GlobalFishingWatch/ssf-tracker-prototype/controller/app/app.py

# Main application

from util import default_logger
from util import load_config
from util import save_config
from util import configure_logger
from config import default_app_state

from statemachine import StateMachine
from statemachine import State
from statemachine import Transition
from statemachine import Event
from button import Button
from timer import Timer
# from gps import MockGPS

from wiring import MockWiring


class App(StateMachine):
    states = [
        State('boot'),
        State('idle', on_enter='on_idle'),
        State('locating', on_enter='on_locating'),
        State('sleep', on_enter='on_sleep'),
    ]
    transitions = [
        Transition(event='reset', source='boot', dest='idle', after='on_reset'),
        Transition(event='idle_timeout', source='idle', dest='sleep', condition='can_deep_sleep'),
        Transition(event='timer_wake', source='sleep', dest='idle'),
        Transition(event='btn_wake', source='sleep', dest='idle'),
        Transition(event='btn1_pressed', after='on_btn1_pressed'),
        Transition(event='btn1_released', after='on_btn1_released'),
        Transition(event='gps_timer', source='idle', dest='locating'),
        Transition(event='gps_ready', source='locating', dest='idle', before='on_gps_ready'),
        Transition(event='gps_timeout', source='locating', dest='idle', before='on_gps_failed'),

        # Catch the gps_timer event in case we were not it the `idle` state and can't transition to `locating` state
        Transition(event='gps_timer', after='retry_event'),
    ]

    @classmethod
    def from_settings(cls, settings, wiring_type=MockWiring, **kwargs):
        app_config = load_config(settings)
        log = configure_logger(app_config)
        wiring = wiring_type(config=app_config)
        log.debug('Creating App...')
        app = cls(wiring=wiring, config=app_config, log=log, **kwargs)
        return app

    def __init__(self, wiring, config=None, log=None, **kwargs):
        self.wiring = wiring
        self.config = config if config else {}
        self.log = log if log else default_logger()
        super(App, self).__init__(states=self.states, transitions=self.transitions, log=self.log, **kwargs)

        self.button1 = Button(name="button1", log=self.log,
                              on_press_event=self.get_event('btn1_pressed'),
                              on_release_event=self.get_event('btn1_released'))

        self.idle_timer = Timer(event=self.get_event('idle_timeout'),
                                duration_ms=self.config.get('IDLE_TIMEOUT_MS', 1000),
                                recurring=True)
        # self.gps = MockGPS(on_ready_event=self.get_event('gps_ready'))
        self.gps_timer = Timer(event=self.get_event('gps_timer'),
                               duration_ms=self.config.get('GPS_FIX_INTERVAL_MS', 10000),
                               recurring=True)
        self.locations = []

    def initialize(self):
        self.log.debug(f'{self.name} initialize...')
        self.wiring.btn_down_event = self.button1.get_event('btn_down')
        self.wiring.btn_up_event = self.button1.get_event('btn_up')
        self.wiring.gps_fix_event = self.get_event('gps_ready')
        self.wiring.initialize()
        wake_reason = self.wiring.wake_reason()
        self.log.debug(f'Wake reason: {wake_reason}')
        if wake_reason == 'RESET':
            self.config['app_state'] = default_app_state
            self.schedule_event('reset')
        self.load_state(self.config['app_state'])

    def settings_file_name(self):
        return self.config['SETTINGS_FILE']

    def is_running(self):
        return True

    def max_sleep_time_ms(self, max_sleep_time_ms):
        next_timer = Timer.get_next_timer()
        return next_timer.time_remaining_ms() if next_timer else max_sleep_time_ms

    def lightsleep(self):
        min_time = self.config.get('MIN_LIGHTSLEEP_TIME_MS', 100)
        max_time = self.config.get('MAX_LIGHTSLEEP_TIME_MS', 1000)
        sleep_time = self.max_sleep_time_ms(max_time)
        if sleep_time > min_time:
            self.wiring.lightsleep(sleep_time)

    def run(self):
        self.log.debug(f'{self.name} run...')
        while self.is_running():
            Timer.check_active_timers()
            Event.trigger_scheduled_events()
            self.gps_update()
            self.lightsleep()

    @staticmethod
    def tick():
        Timer.check_active_timers()
        Event.trigger_scheduled_events()

    def on_reset(self, event):
        self.gps_timer.reset()

    def on_idle(self, event):
        self.idle_timer.reset()

    def can_deep_sleep(self, event):
        # can't sleep if
        #    the button is pressed
        #    we are getting a gps fix
        #    we are transmitting a message
        #    there is not enough time before the next timer goes off (because it takes time to restart)

        min_time = self.config.get('MIN_DEEPSLEEP_TIME_MS', 10 * 1000)
        max_time = self.config.get('MAX_DEEPSLEEP_TIME_MS', 10 * 1000)
        sleep_time = self.max_sleep_time_ms(max_time)

        sleep_blocked = (
            self.button1.state.name == 'pressed'
            or self.state.name in ('locating', 'transmitting')
            or sleep_time < min_time
        )
        return not sleep_blocked

    def on_sleep(self, event):
        self.idle_timer.cancel()

        max_deep_sleep_time = self.config.get('MAX_DEEPSLEEP_TIME_MS', 10*1000)

        sleep_time = self.max_sleep_time_ms(max_deep_sleep_time)
        self.config['app_state'] = self.save_state()
        filename = self.settings_file_name()
        if filename:
            save_config(self.config, self.settings_file_name)
        else:
            self.log.debug('Unable to save settings before sleep because no file name is configured')

        # NB: this will sleep for the specified time and then reset the app
        # NB: Control flow will never return from this call unless you are using MockWiring
        self.wiring.deepsleep(sleep_time)

    def on_btn1_pressed(self, event):
        self.wiring.led1 = 1

    def on_btn1_released(self, event):
        self.wiring.led1 = 0

    def on_locating(self, event):
        # start to fix a new gps location
        # self.gps.schedule_event('locate')
        self.wiring.gps_wake()

    def retry_event(self, event):
        # retry an event after a delay
        t = Timer(duration_ms=self.config['RETRY_INTERVAL_MS'],
                  event=event)
        t.reset()

    def on_gps_ready(self, event):
        # self.locations.append(self.gps.last_location)
        # self.gps.schedule_event('sleep')
        location = event.kwargs
        if location:
            self.locations.append(location)
            self.log.debug(location.get('sentence', 'unknown message in gps_ready event'))
        self.wiring.gps_sleep()

    def on_gps_failed(self, event):
        # self.gps.schedule_event('sleep')
        self.wiring.gps_sleep()

    def gps_update(self):
        message = self.wiring.gps_update()
        if message and 'sentence' in message:
            self.log.info(message['message'])

    def save_state(self):
        state = super(App, self).save_state()
        state['button1'] = self.button1.save_state()
        state['idle_timer'] = self.idle_timer.save_state()
        state['gps_timer'] = self.gps_timer.save_state()
        state['locations'] = self.locations
        return state

    def load_state(self, state):
        self.button1.load_state(state['button1'])
        self.idle_timer.load_state(state['idle_timer'])
        self.gps_timer.load_state(state['gps_timer'])
        self.locations = state['locations']
        super(App, self).load_state(state)
